mancio/Volante-The-Gamepad/Assetto Corsa/Lotus GT Dream/asphalt.PNG

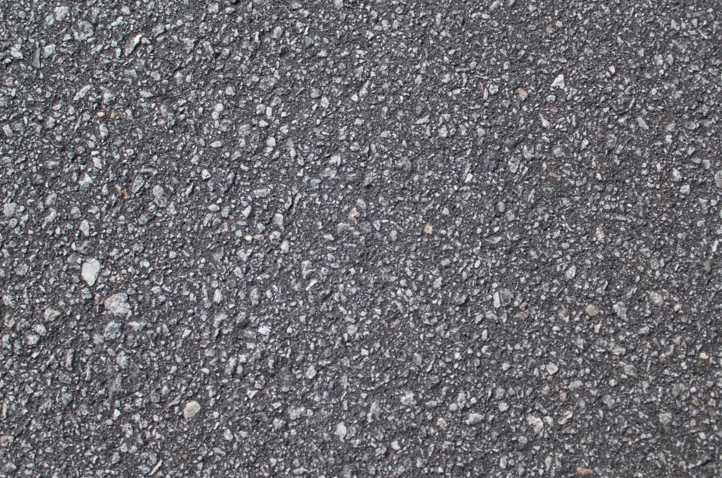
Assetto Corsa/Lotus GT Dream/asphalt.PNG
