mancio/Volante-The-Gamepad/Assetto Corsa/Lotus GT Dream/back.jpg

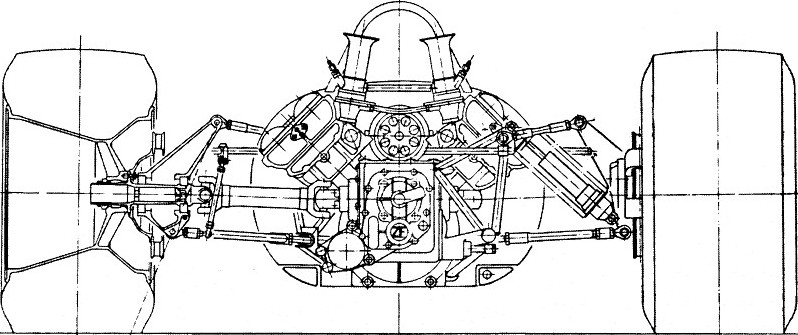
Assetto Corsa/Lotus GT Dream/back.jpg
