mancio/Volante-The-Gamepad/Assetto Corsa/Lotus GT Dream/brembo.jpg

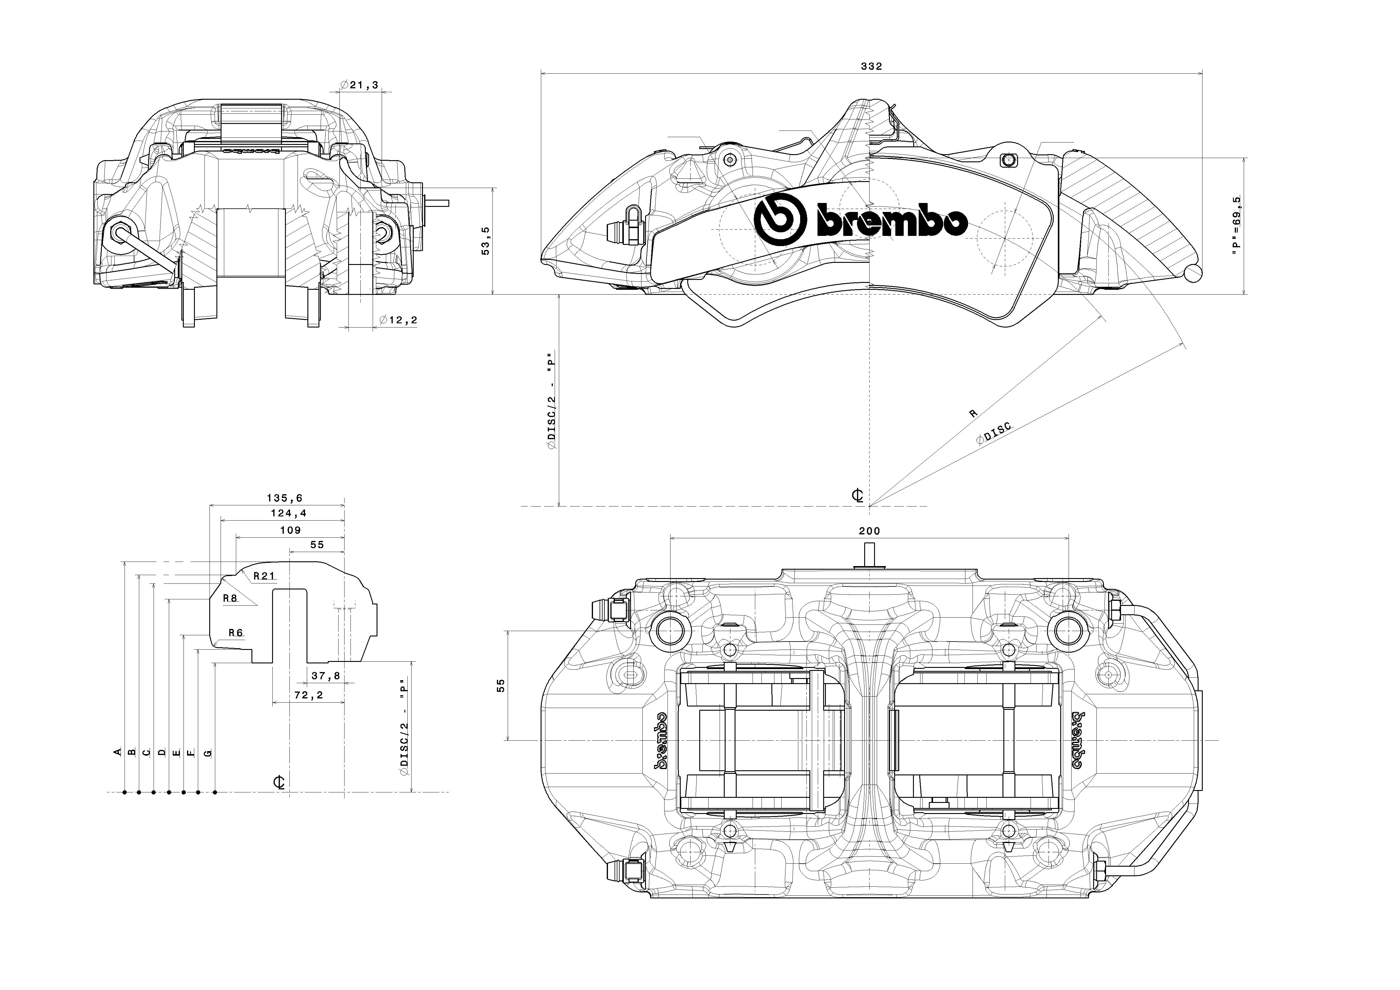
Assetto Corsa/Lotus GT Dream/brembo.jpg
