mancio/Volante-The-Gamepad/Assetto Corsa/Lotus GT Dream/brembo_side.jpg

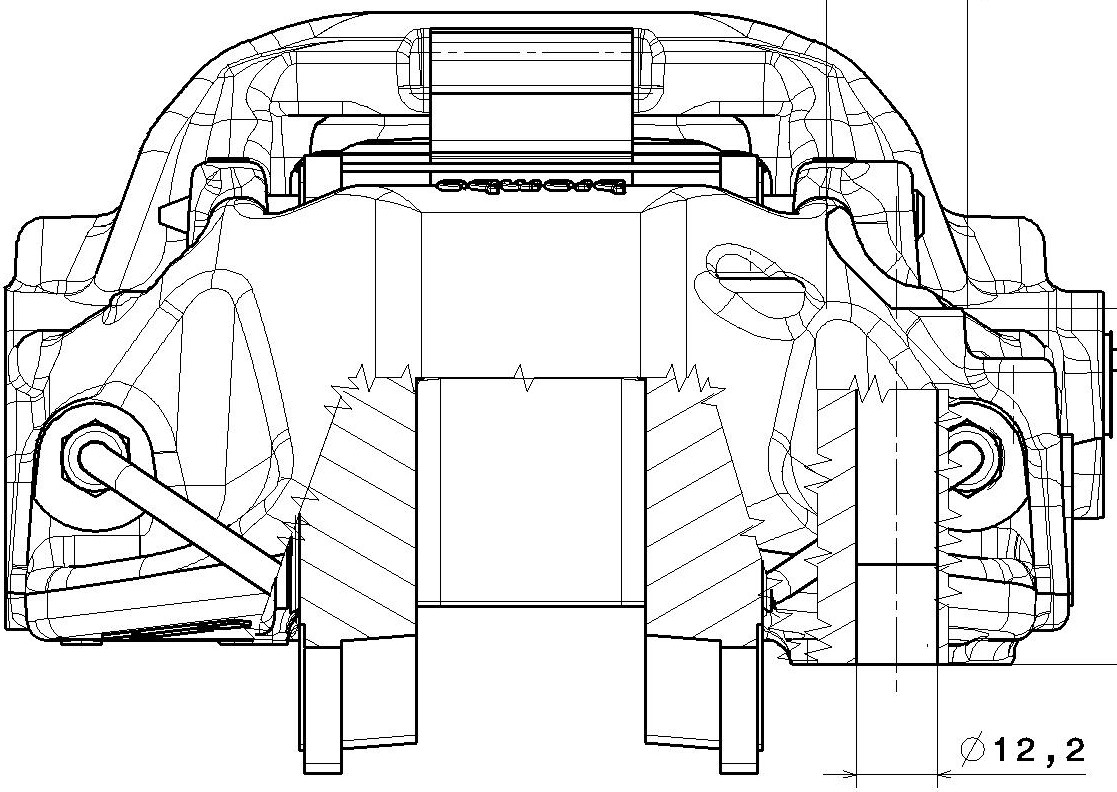
Assetto Corsa/Lotus GT Dream/brembo_side.jpg
