mancio/Volante-The-Gamepad/Assetto Corsa/Lotus GT Dream/brembo_top.jpg

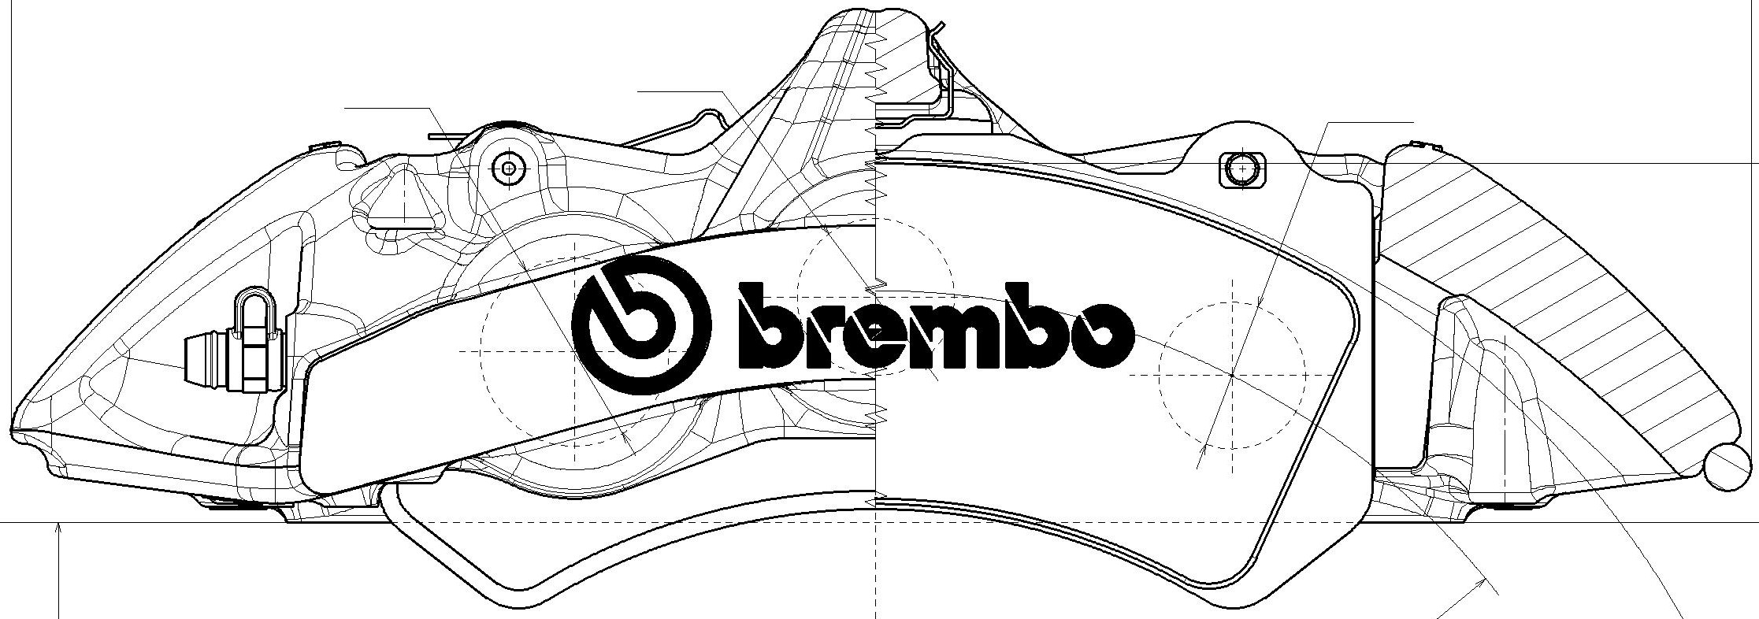
Assetto Corsa/Lotus GT Dream/brembo_top.jpg
