mancio/Volante-The-Gamepad/Assetto Corsa/Lotus GT Dream/engine.png

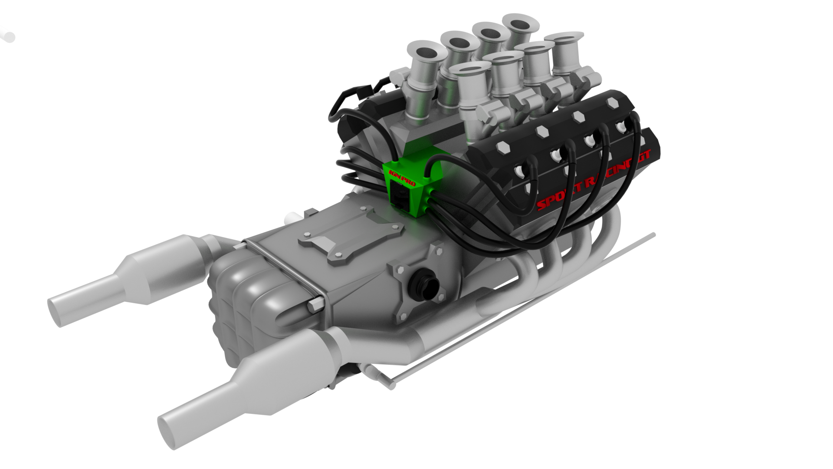
Assetto Corsa/Lotus GT Dream/engine.png
