mancio/Volante-The-Gamepad/Assetto Corsa/Lotus GT Dream/engine_back.jpg

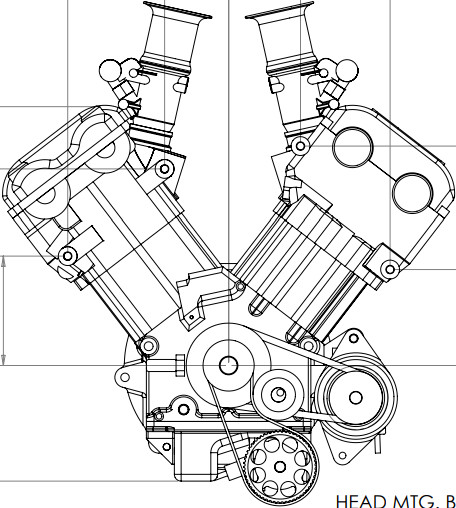
Assetto Corsa/Lotus GT Dream/engine_back.jpg
