mancio/Volante-The-Gamepad/Assetto Corsa/Lotus GT Dream/engine_diag.jpg

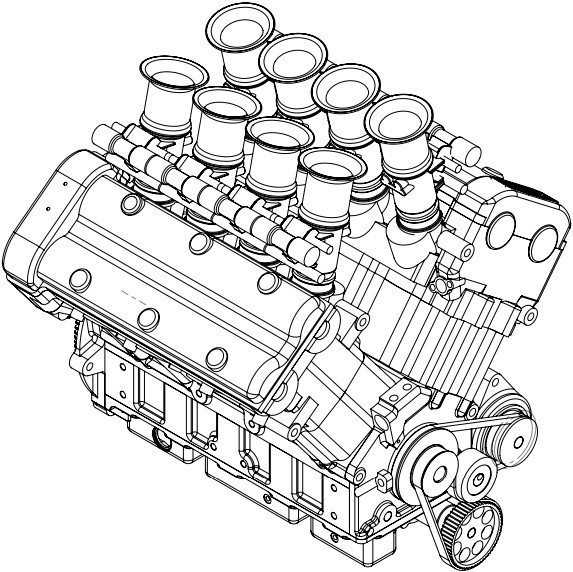
Assetto Corsa/Lotus GT Dream/engine_diag.jpg
