mancio/Volante-The-Gamepad/Assetto Corsa/Lotus GT Dream/engine_fr.jpg

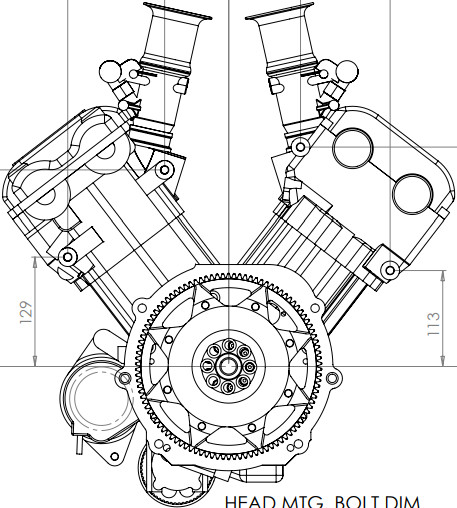
Assetto Corsa/Lotus GT Dream/engine_fr.jpg
