mancio/Volante-The-Gamepad/Assetto Corsa/Lotus GT Dream/engine_side.jpg

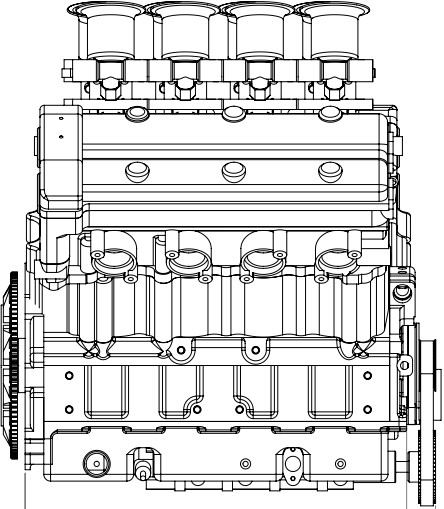
Assetto Corsa/Lotus GT Dream/engine_side.jpg
