mancio/Volante-The-Gamepad/Assetto Corsa/Lotus GT Dream/engine_top.jpg

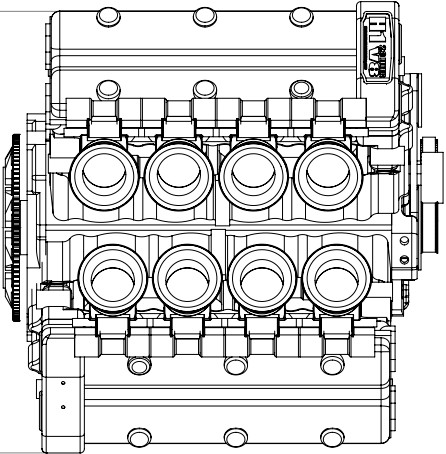
Assetto Corsa/Lotus GT Dream/engine_top.jpg
