mancio/Volante-The-Gamepad/Assetto Corsa/Lotus GT Dream/exaust.PNG

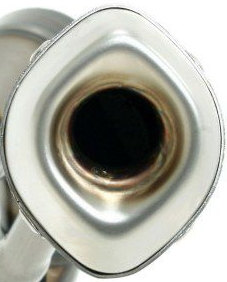
Assetto Corsa/Lotus GT Dream/exaust.PNG
