mancio/Volante-The-Gamepad/Assetto Corsa/Lotus GT Dream/front.jpg

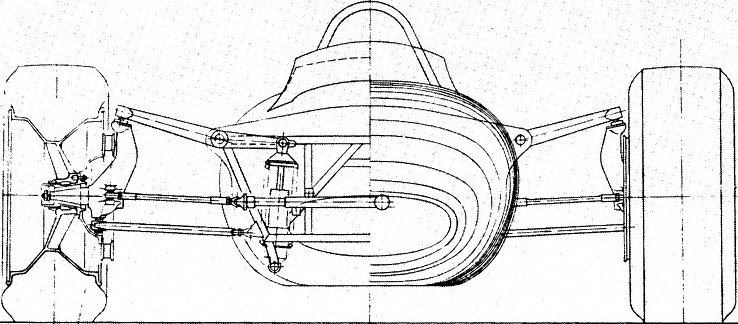
Assetto Corsa/Lotus GT Dream/front.jpg
