mancio/Volante-The-Gamepad/Assetto Corsa/Lotus GT Dream/lambo_rim.jpg

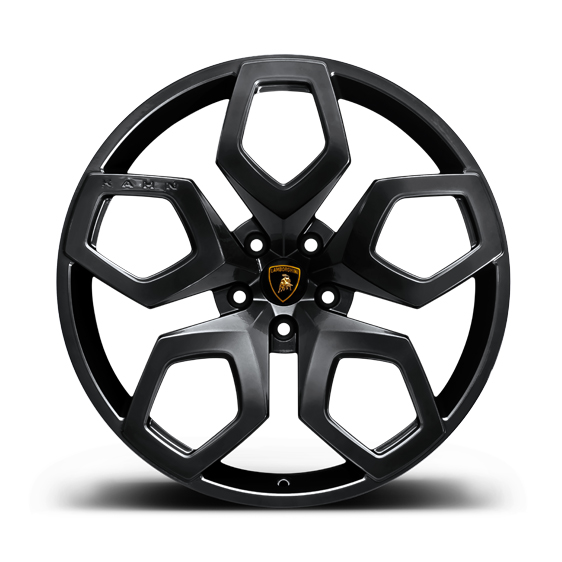
Assetto Corsa/Lotus GT Dream/lambo_rim.jpg
