mancio/Volante-The-Gamepad/Assetto Corsa/Lotus GT Dream/lotus-49-gp.gif

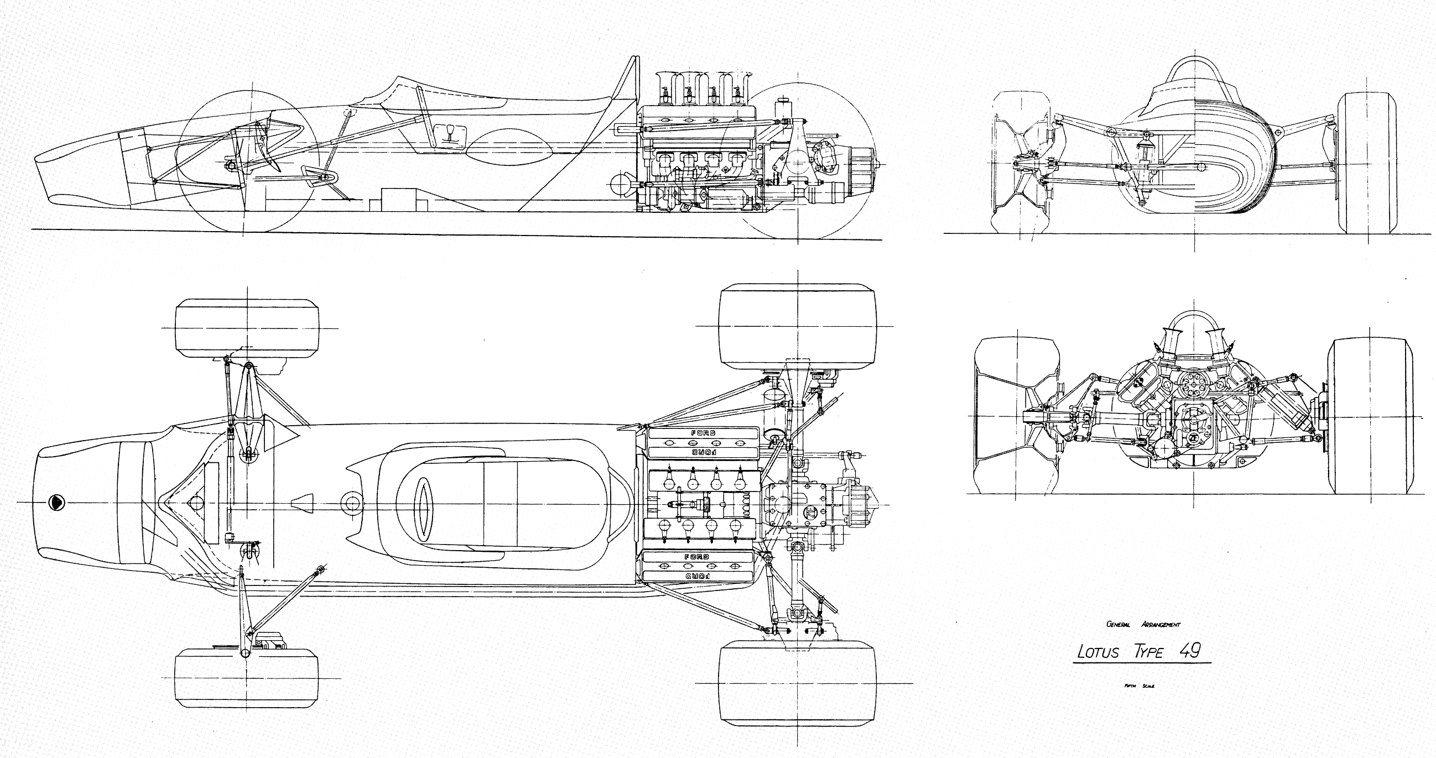
Assetto Corsa/Lotus GT Dream/lotus-49-gp.gif
