mancio/Volante-The-Gamepad/Assetto Corsa/Lotus GT Dream/prova2.png

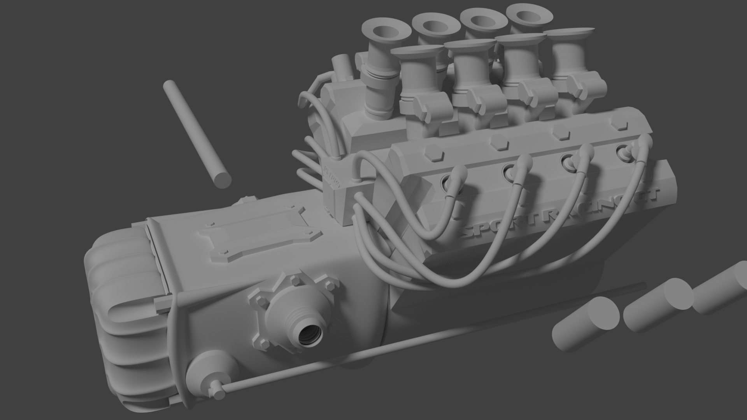
Assetto Corsa/Lotus GT Dream/prova2.png
