mancio/Volante-The-Gamepad/Assetto Corsa/Lotus GT Dream/prova.png

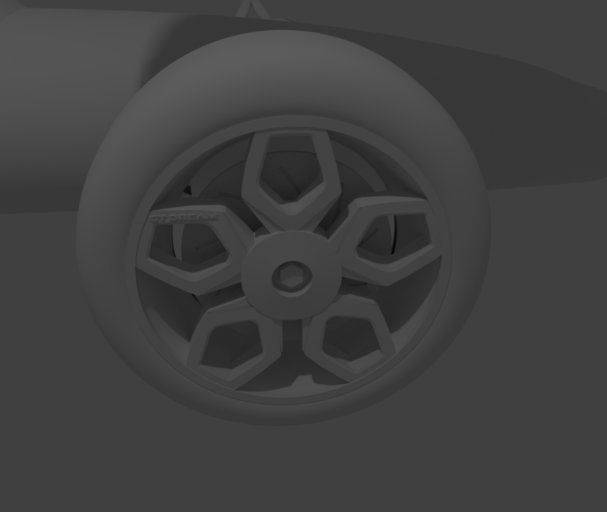
Assetto Corsa/Lotus GT Dream/prova.png
