mancio/Volante-The-Gamepad/Assetto Corsa/Lotus GT Dream/side.jpg

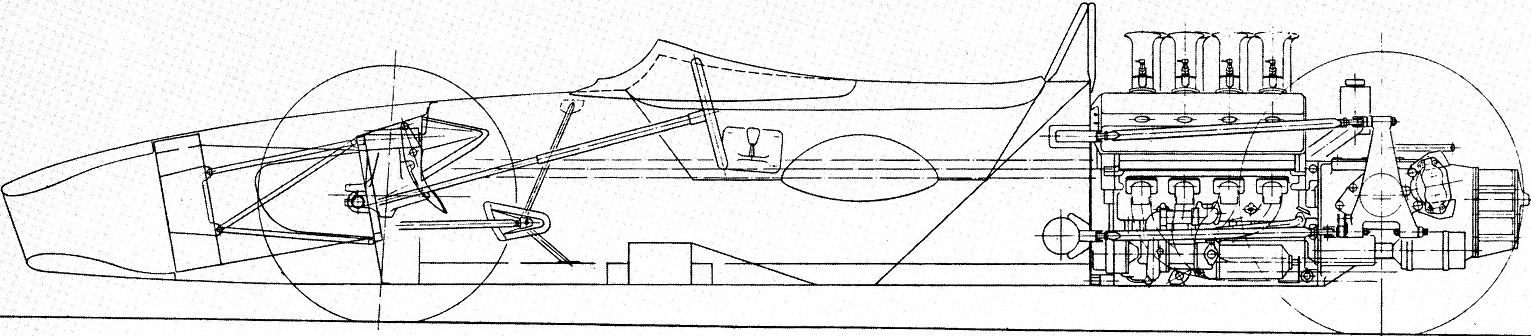
Assetto Corsa/Lotus GT Dream/side.jpg
