mancio/Volante-The-Gamepad/Assetto Corsa/Lotus GT Dream/spark.PNG

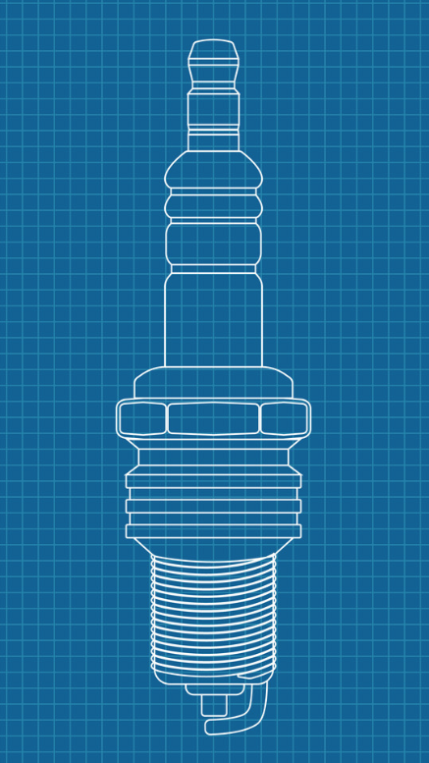
Assetto Corsa/Lotus GT Dream/spark.PNG
