mancio/Volante-The-Gamepad/Assetto Corsa/Lotus GT Dream/steering.png

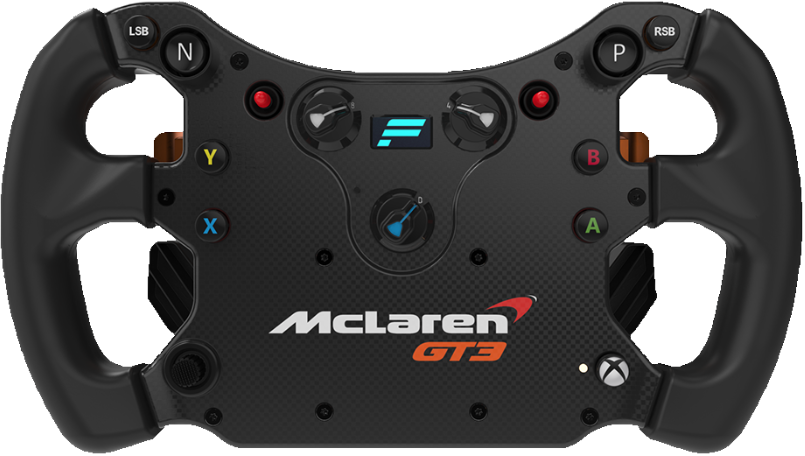
Assetto Corsa/Lotus GT Dream/steering.png
