mancio/Volante-The-Gamepad/Assetto Corsa/Lotus GT Dream/suspension.PNG

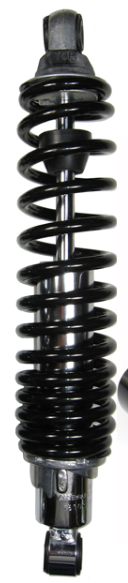
Assetto Corsa/Lotus GT Dream/suspension.PNG
