mancio/Volante-The-Gamepad/Assetto Corsa/Lotus GT Dream/top.jpg

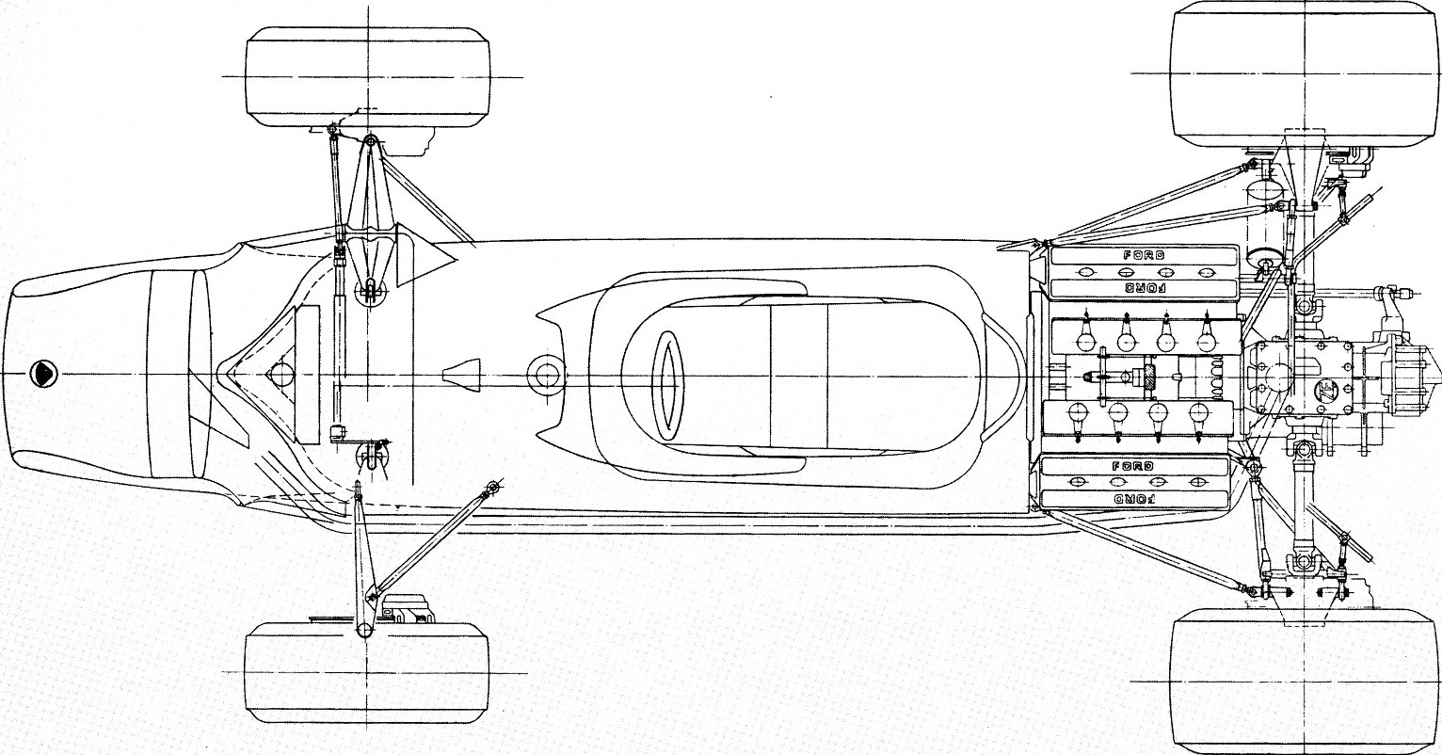
Assetto Corsa/Lotus GT Dream/top.jpg
