mancio/Volante-The-Gamepad/Fritzing/Touchbutton_bb.jpg

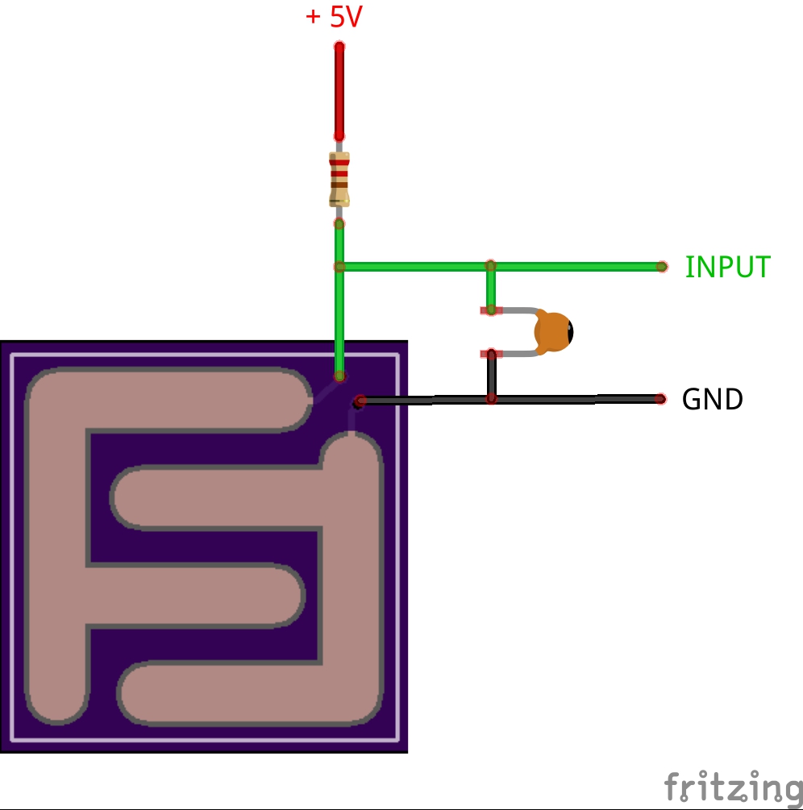
Fritzing/Touchbutton_bb.jpg
