mancio/Volante-The-Gamepad/Fritzing/Volante breadboard.jpg

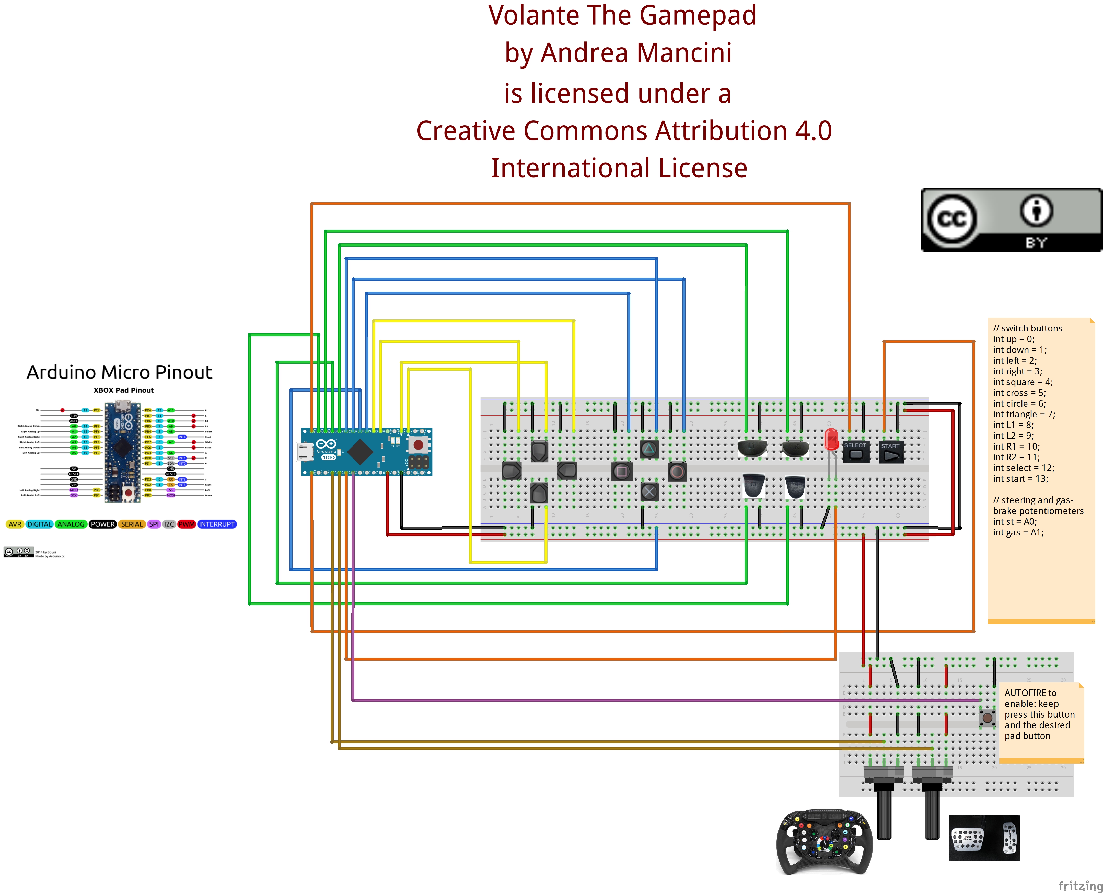
Fritzing/Volante breadboard.jpg
