mancio/Volante-The-Gamepad/Gamepad 3d design/button.PNG

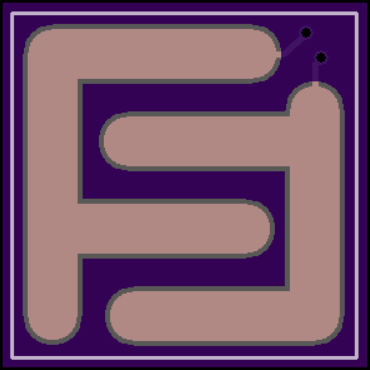
Gamepad 3d design/button.PNG
