mancio/Volante-The-Gamepad/Gamepad 3d design/open.PNG

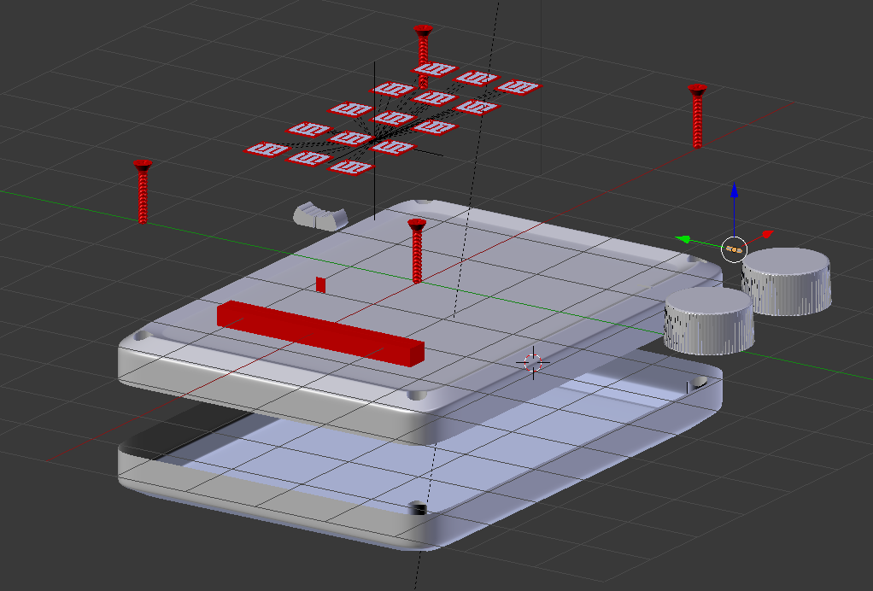
Gamepad 3d design/open.PNG
