mancio/Volante-The-Gamepad/Gamepad 3d design/wire.PNG

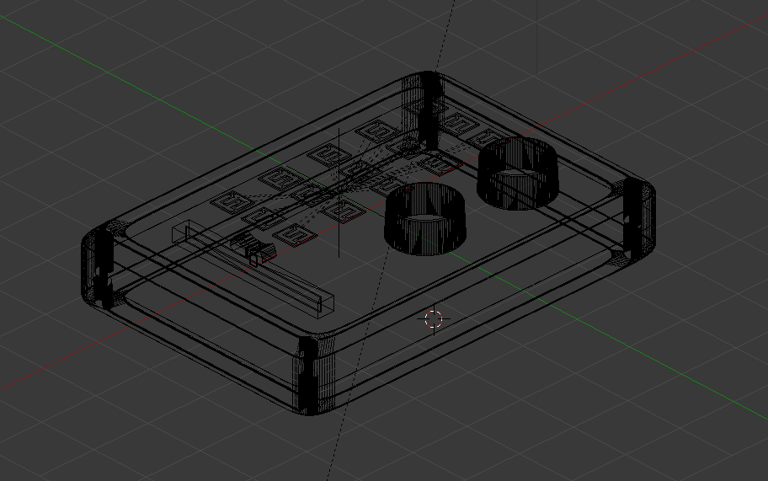
Gamepad 3d design/wire.PNG
