mancio/Volante-The-Gamepad/kicad/shield/B.Cu.PNG

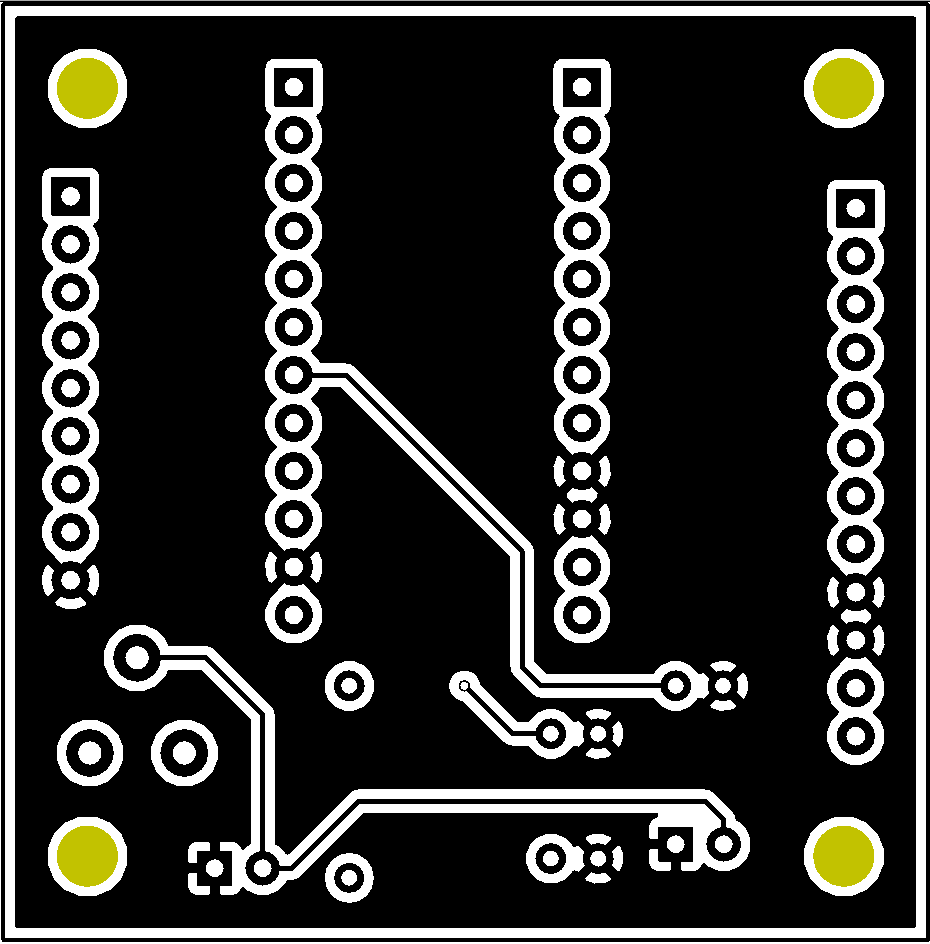
kicad/shield/B.Cu.PNG
