mancio/Volante-The-Gamepad/kicad/shield/F.Cu.PNG

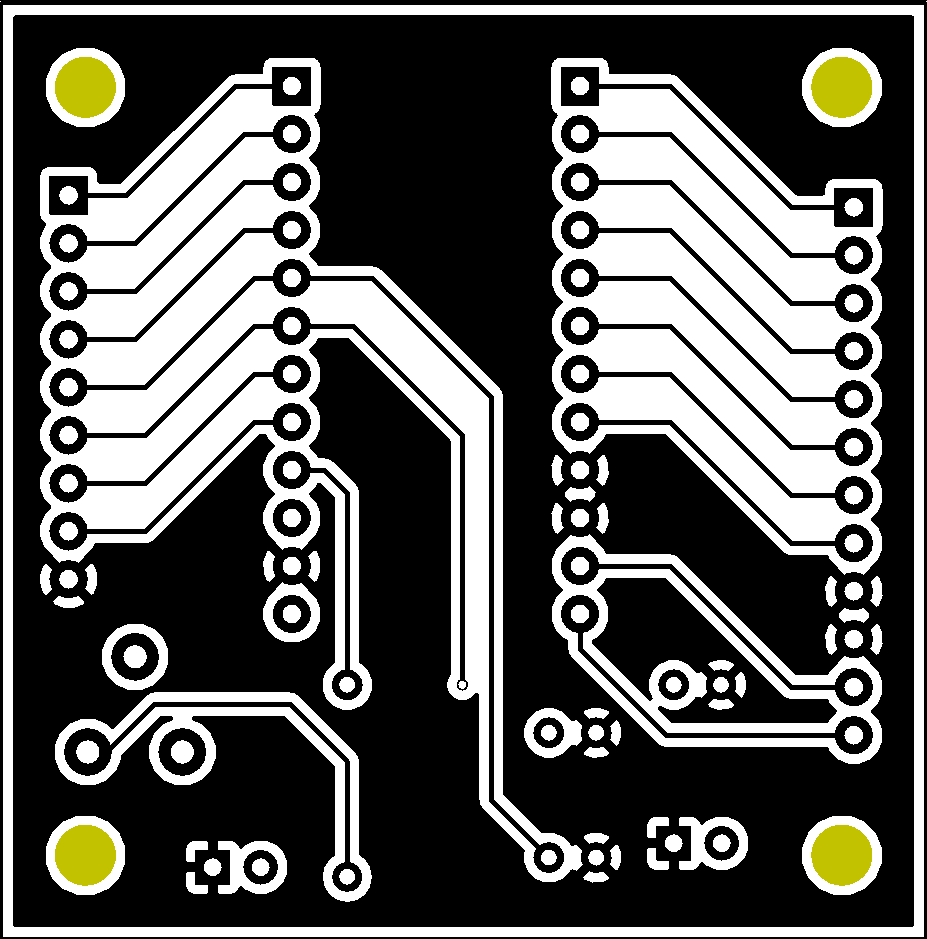
kicad/shield/F.Cu.PNG
