mancio/Volante-The-Gamepad/Picture/alt.PNG

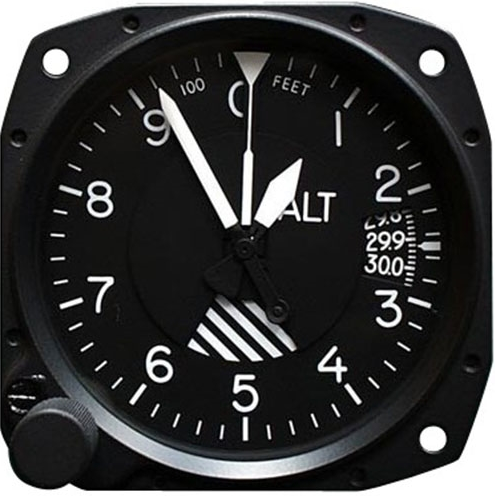
Picture/alt.PNG
