mancio/Volante-The-Gamepad/Picture/assetto2.jpg

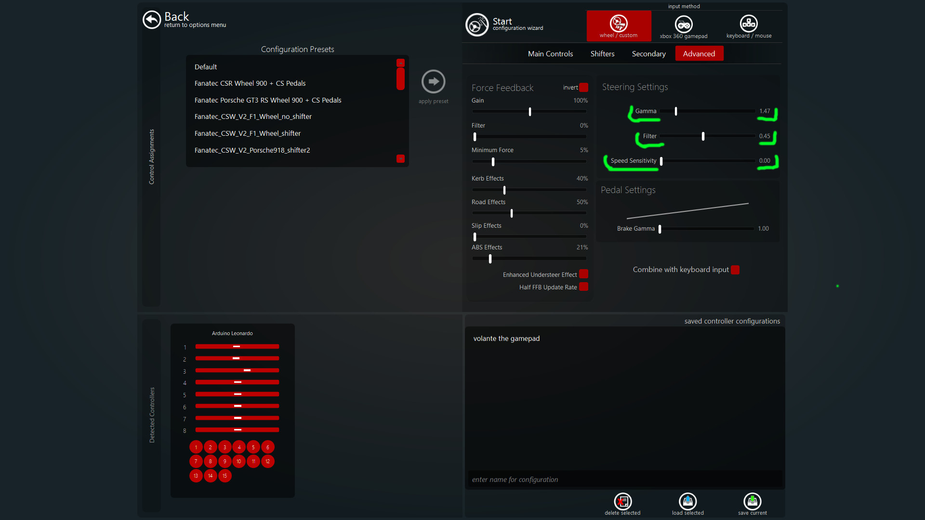
Picture/assetto2.jpg
