mancio/Volante-The-Gamepad/Picture/assetto.jpg

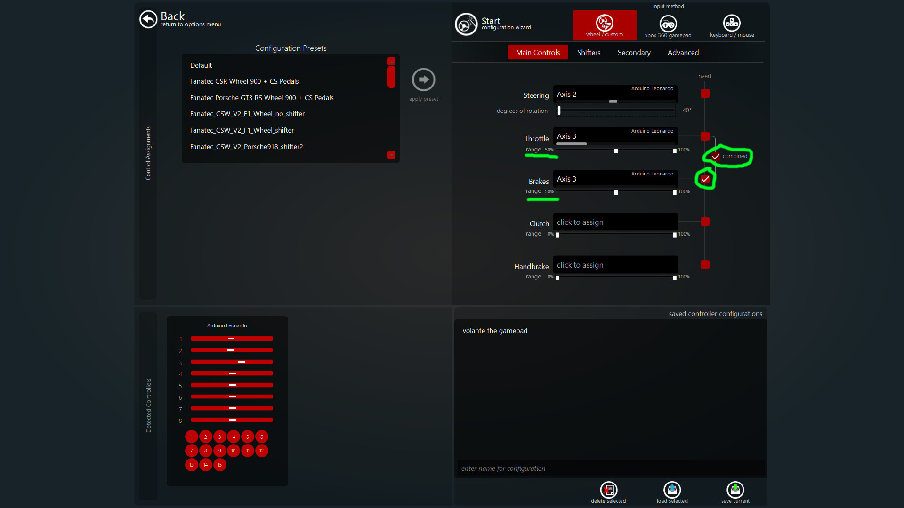
Picture/assetto.jpg
