mancio/Volante-The-Gamepad/Picture/cap_box.jpg

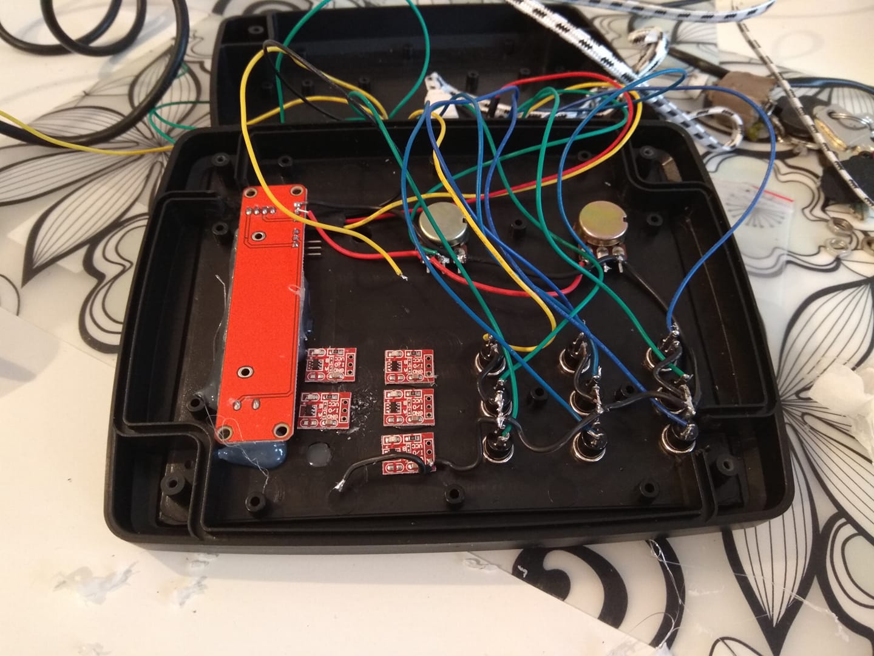
Picture/cap_box.jpg
