mancio/Volante-The-Gamepad/Picture/first_box.jpg

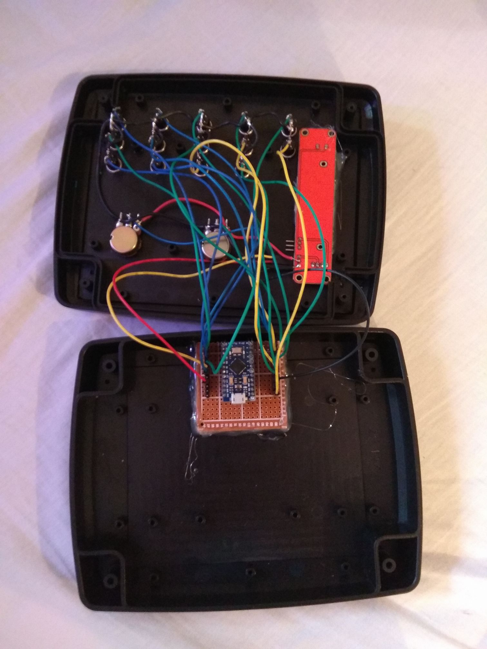
Picture/first_box.jpg
