mancio/Volante-The-Gamepad/Picture/L2.PNG

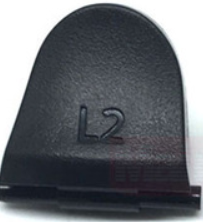
Picture/L2.PNG
