mancio/Volante-The-Gamepad/Picture/led_pins.jpg

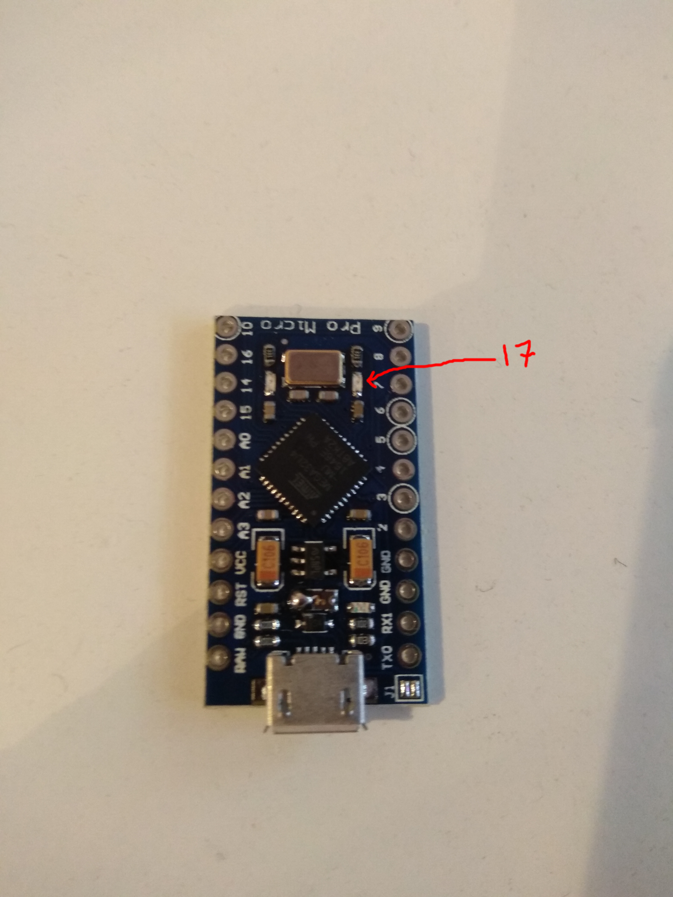
Picture/led_pins.jpg
