mancio/Volante-The-Gamepad/Picture/new_board.jpg

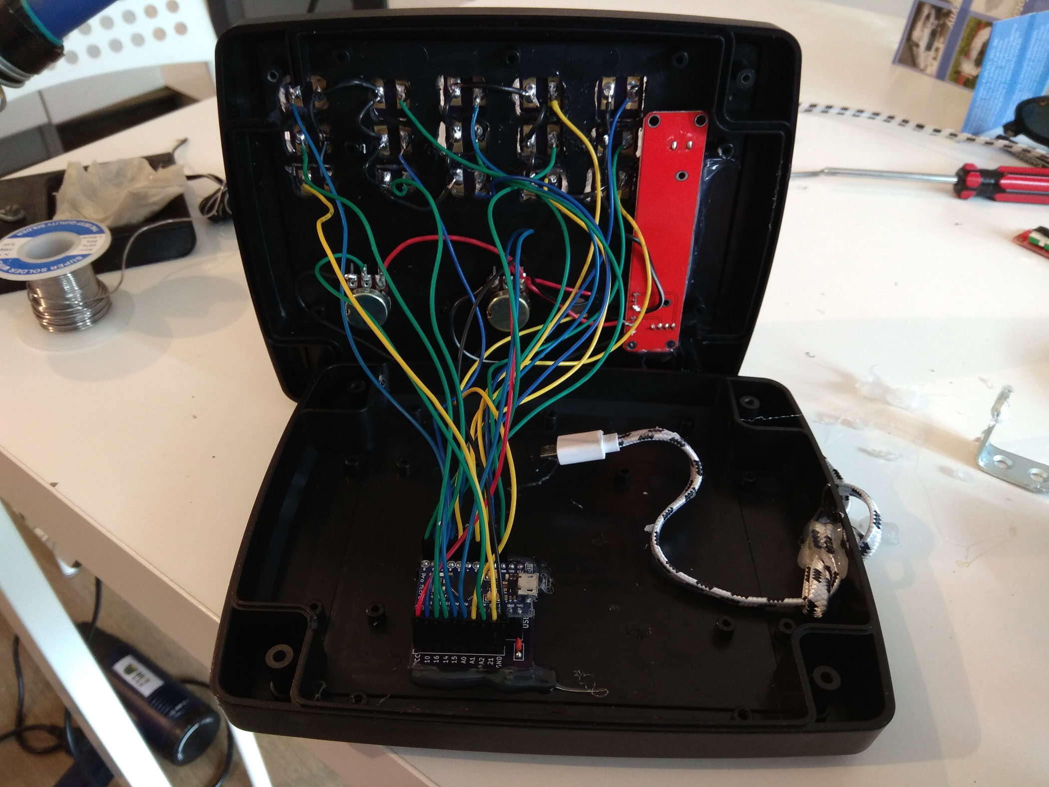
Picture/new_board.jpg
