mancio/Volante-The-Gamepad/Picture/pad_layout_draft.png

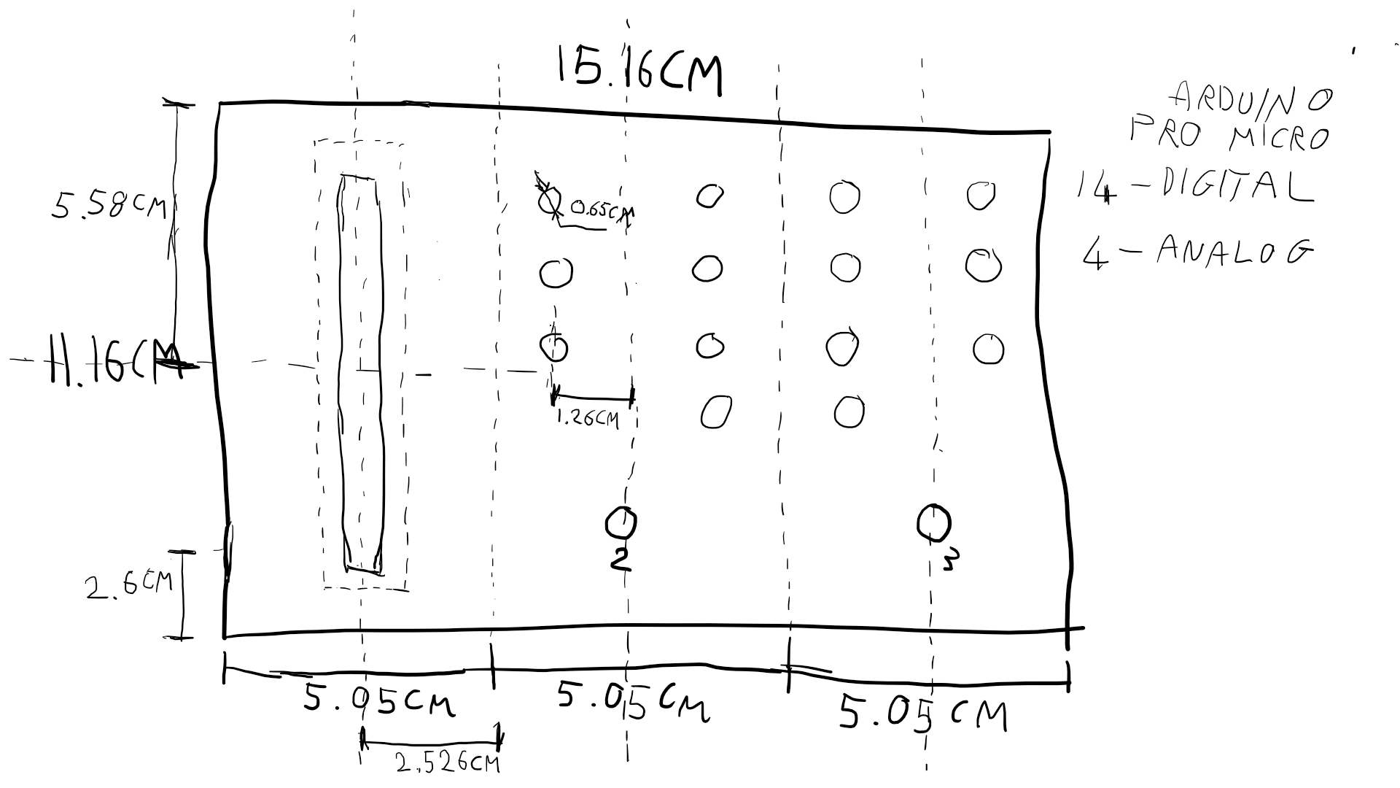
Picture/pad_layout_draft.png
