mancio/Volante-The-Gamepad/Picture/pcb2_rear.jpg

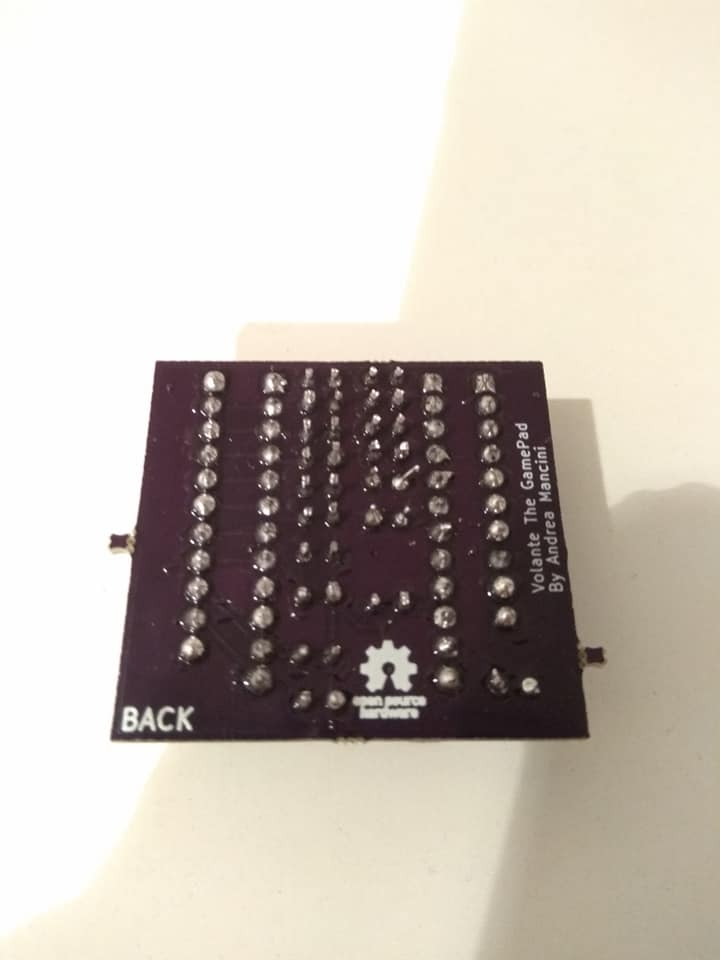
Picture/pcb2_rear.jpg
