mancio/Volante-The-Gamepad/Picture/pcb_shield_module.jpg

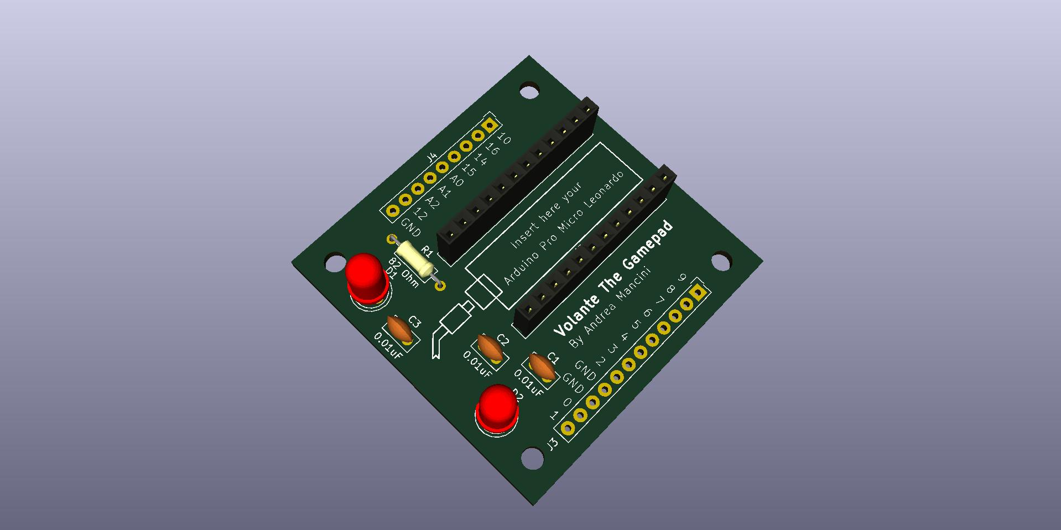
Picture/pcb_shield_module.jpg
