mancio/Volante-The-Gamepad/Picture/R2.PNG

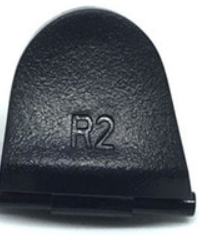
Picture/R2.PNG
