mancio/Volante-The-Gamepad/Picture/touch_button_simple_rear.PNG

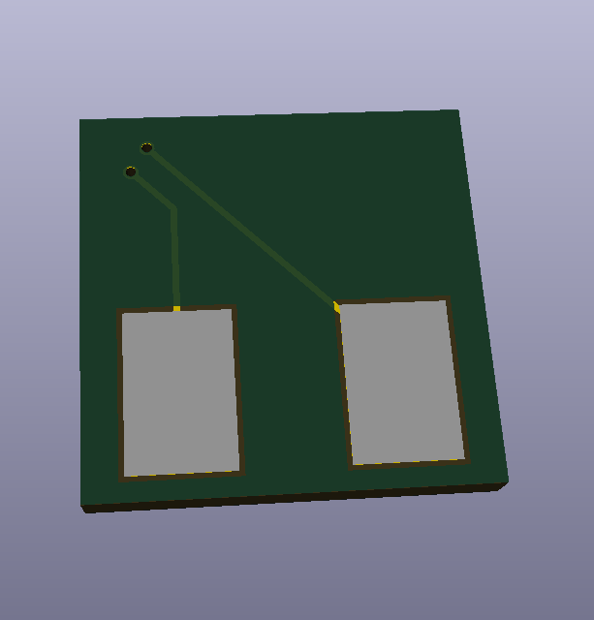
Picture/touch_button_simple_rear.PNG
