mancio/Volante-The-Gamepad/manual/padd.png

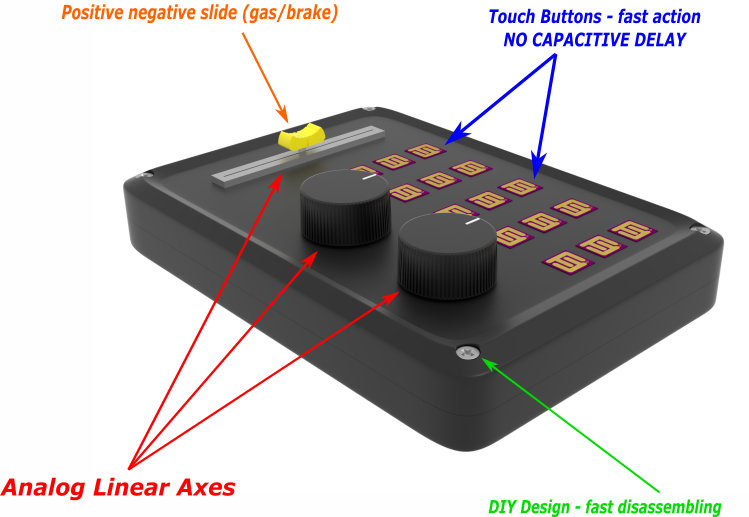
manual/padd.png
