mancio/Volante-The-Gamepad/Assetto Corsa/Lotus GT Dream/test.png

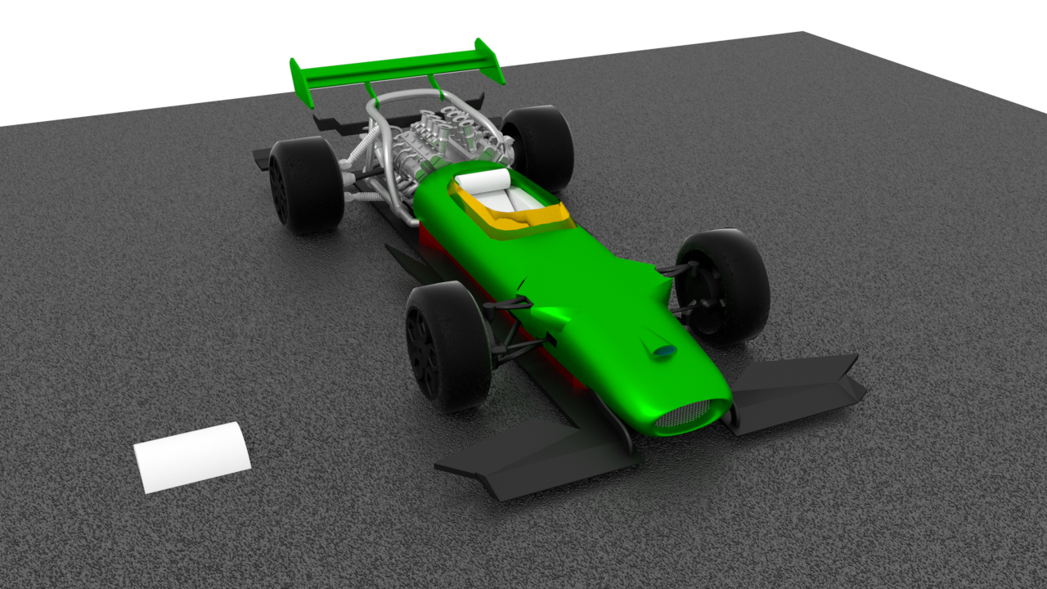
Assetto Corsa/Lotus GT Dream/test.png
